chrisys/train-departure-display/assets/pi-display-connections_bb.png

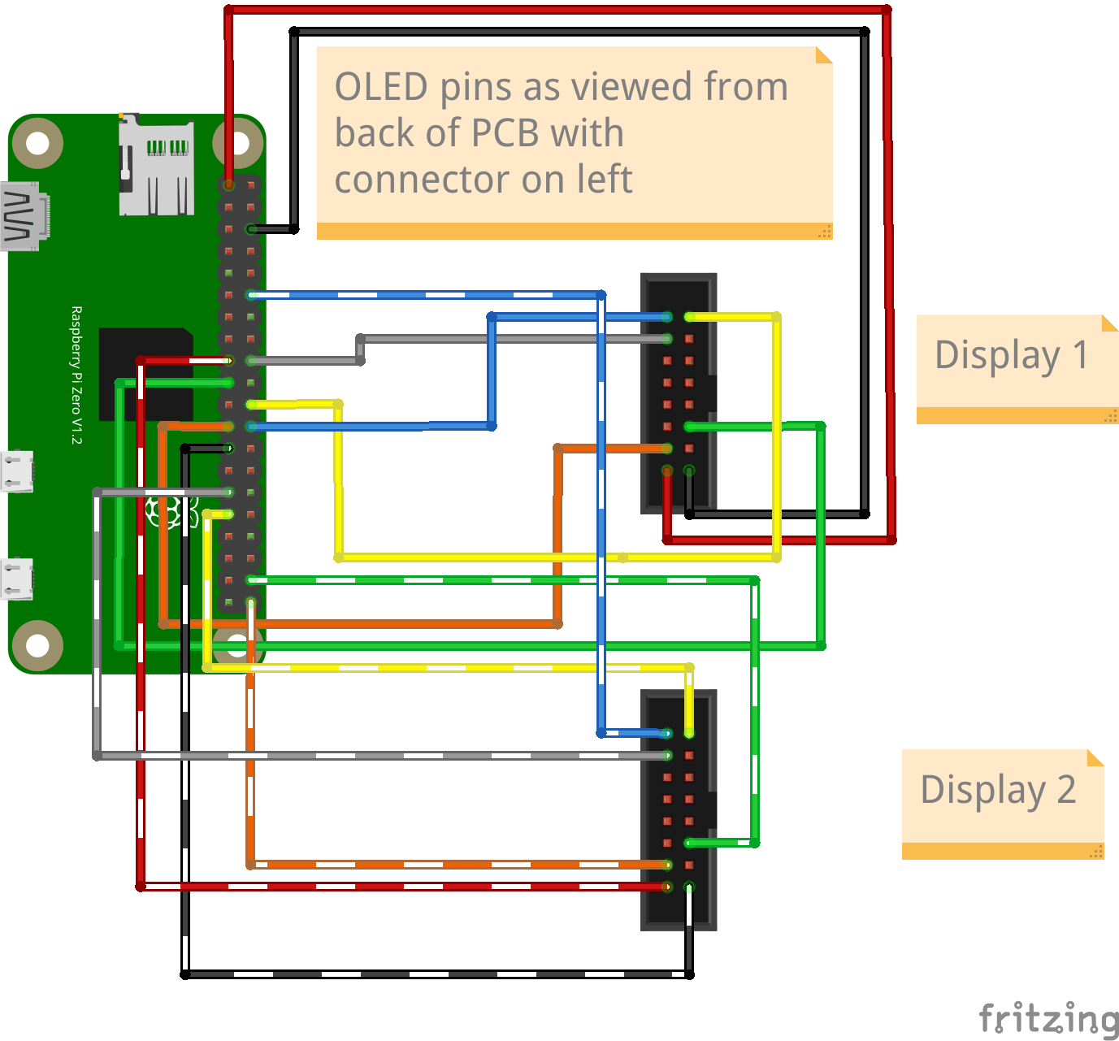
assets/pi-display-connections_bb.png
